Bellafaire/ESP32-Smart-Watch/Pictures and Videos/20191118_123628.jpg

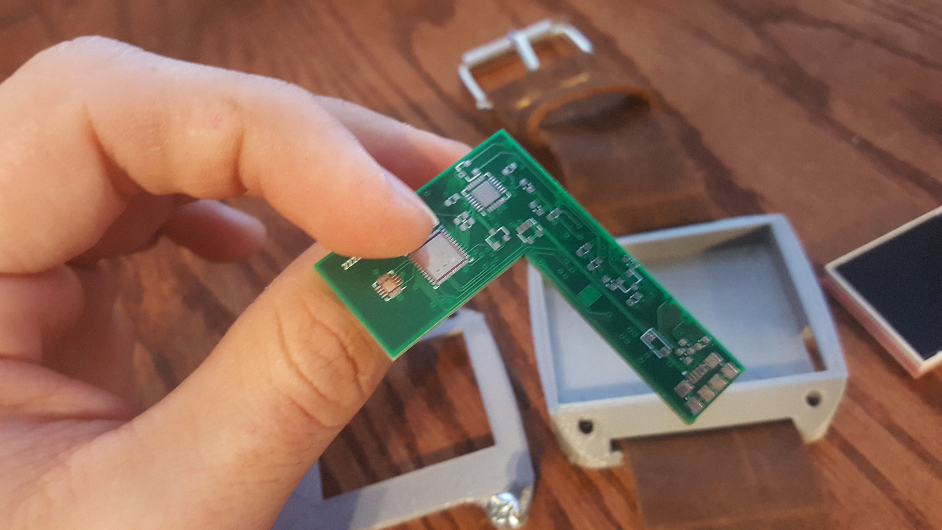
Pictures and Videos/20191118_123628.jpg
