Bellafaire/ESP32-Smart-Watch/Pictures and Videos/20191118_124004.jpg

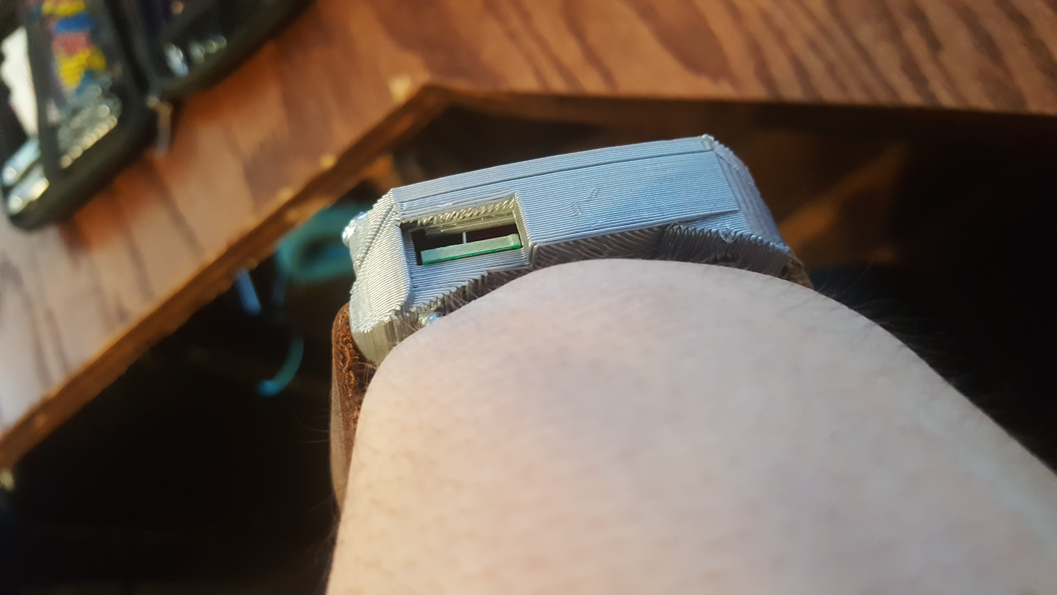
Pictures and Videos/20191118_124004.jpg
