Bellafaire/ESP32-Smart-Watch/Pictures and Videos/20200519_230237.jpg

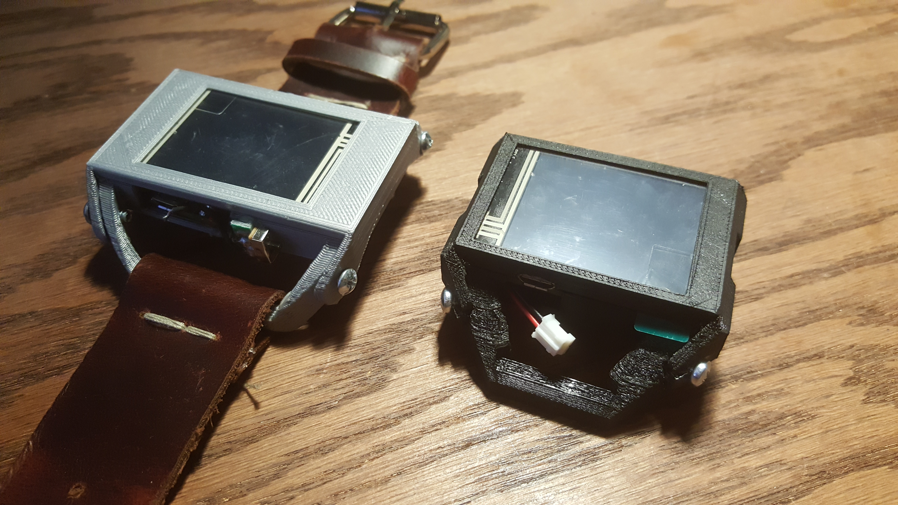
Pictures and Videos/20200519_230237.jpg
