Bellafaire/ESP32-Smart-Watch/Pictures and Videos/20200519_230911.jpg

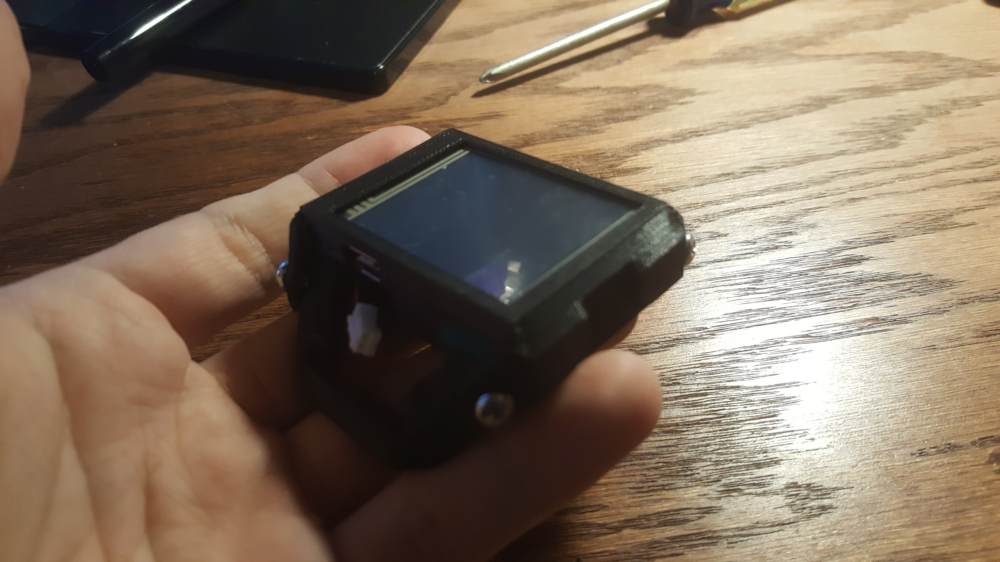
Pictures and Videos/20200519_230911.jpg
