Bellafaire/ESP32-Smart-Watch/Pictures and Videos/20200519_233520.jpg

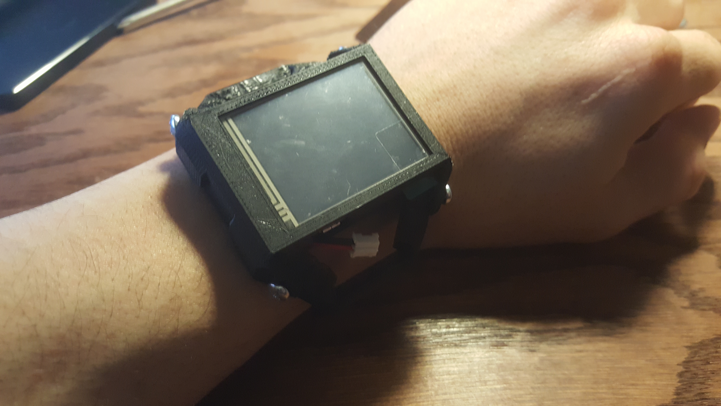
Pictures and Videos/20200519_233520.jpg
