Bellafaire/ESP32-Smart-Watch/Pictures and Videos/20200614_194343.jpg

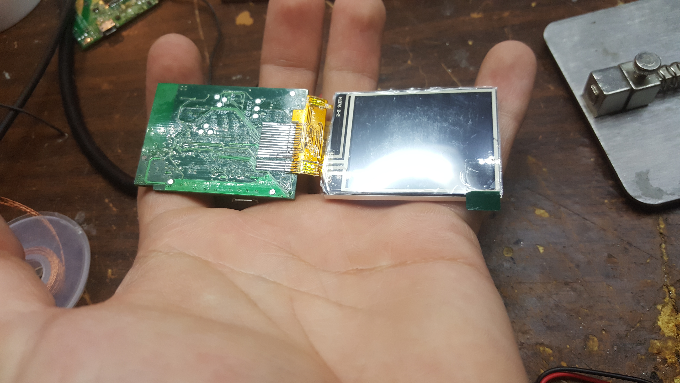
Pictures and Videos/20200614_194343.jpg
