Bellafaire/ESP32-Smart-Watch/Pictures and Videos/20200614_194347.jpg

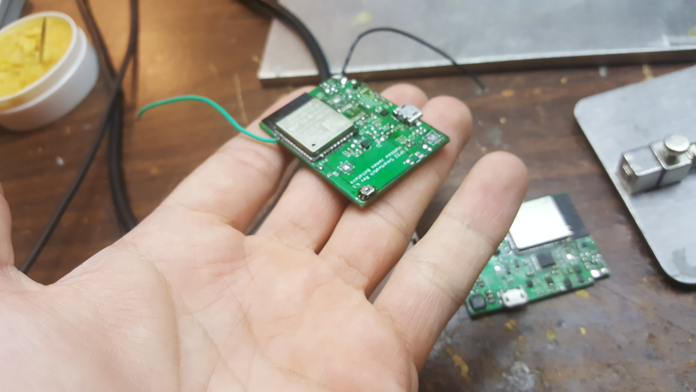
Pictures and Videos/20200614_194347.jpg
