Bellafaire/ESP32-Smart-Watch/Pictures and Videos/IMG_20200818_204534.jpg

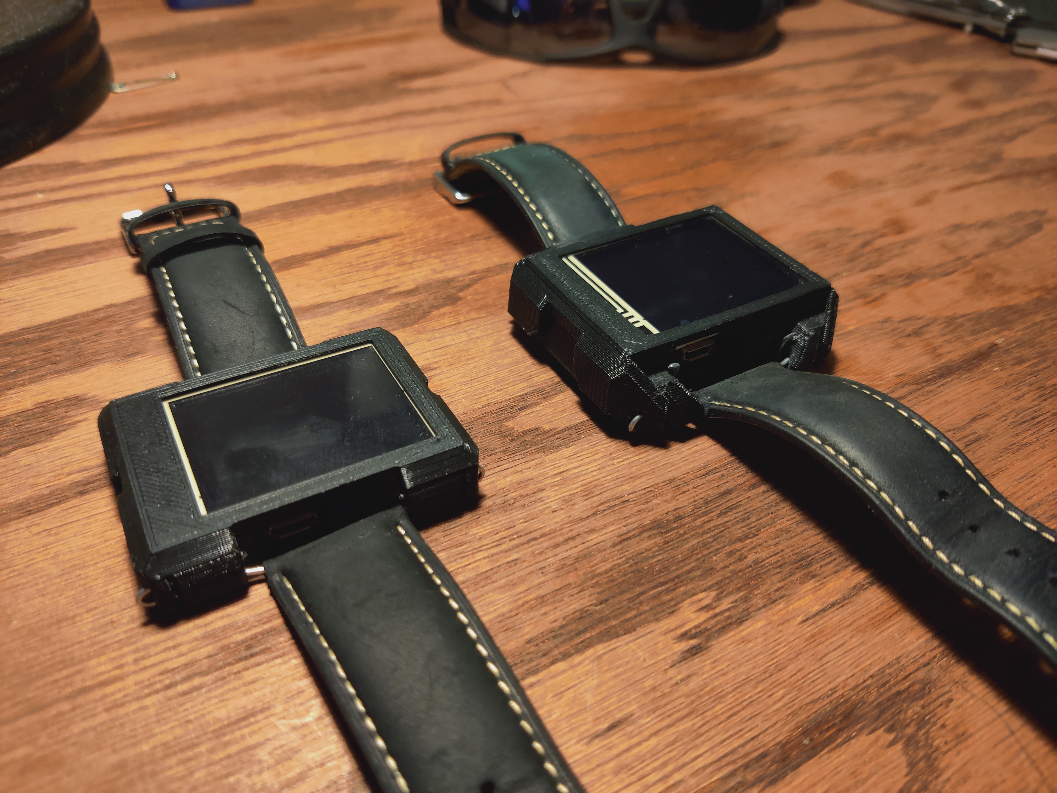
Pictures and Videos/IMG_20200818_204534.jpg
