Bellafaire/ESP32-Smart-Watch/Pictures and Videos/IMG_20200818_204633.jpg

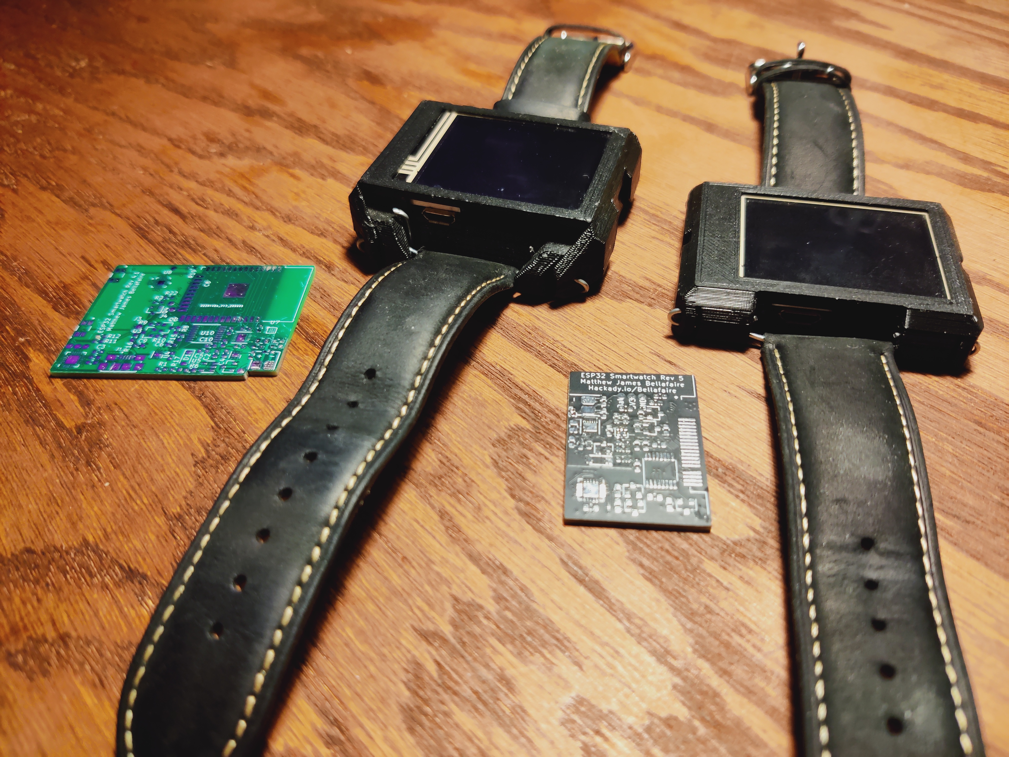
Pictures and Videos/IMG_20200818_204633.jpg
