Bellafaire/ESP32-Smart-Watch/Pictures and Videos/IMG_20200818_2127321.jpg

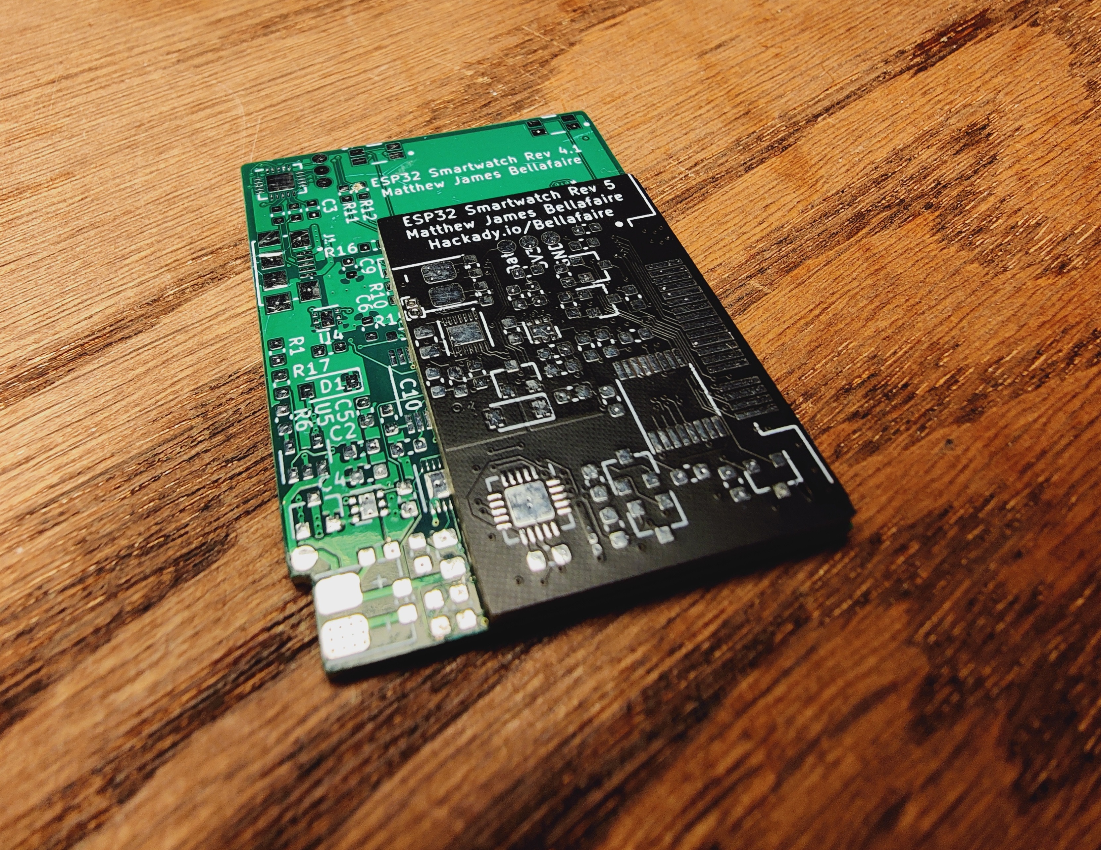
Pictures and Videos/IMG_20200818_2127321.jpg
