Bellafaire/ESP32-Smart-Watch/Pictures and Videos/Screenshot_1 (2).png

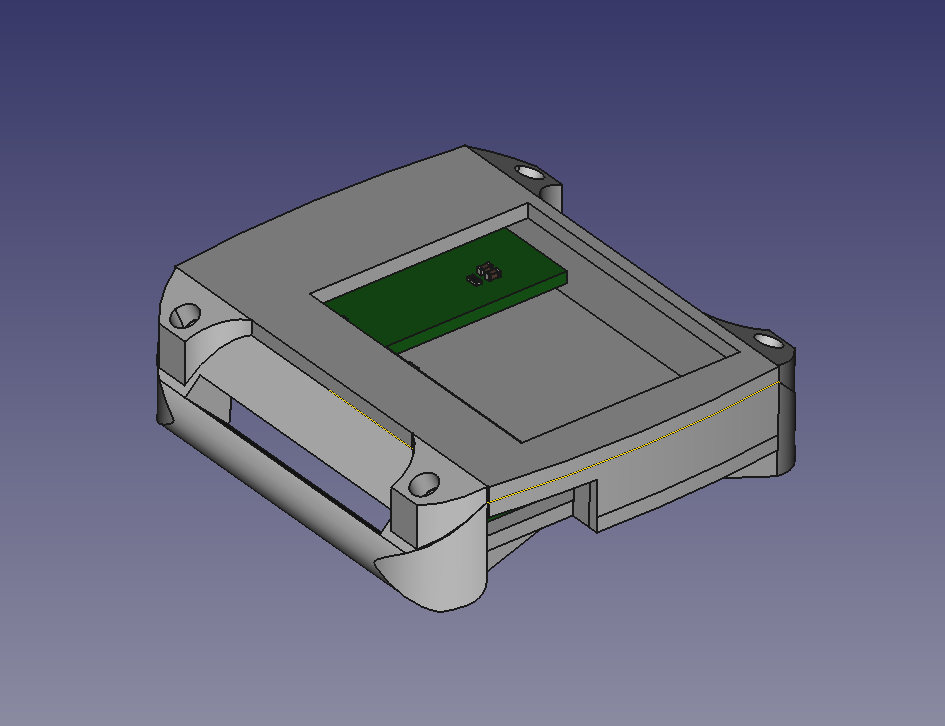
Pictures and Videos/Screenshot_1 (2).png
