Bellafaire/ESP32-Smart-Watch/Pictures and Videos/vlcsnap-2020-08-18-21h04m51s279.png

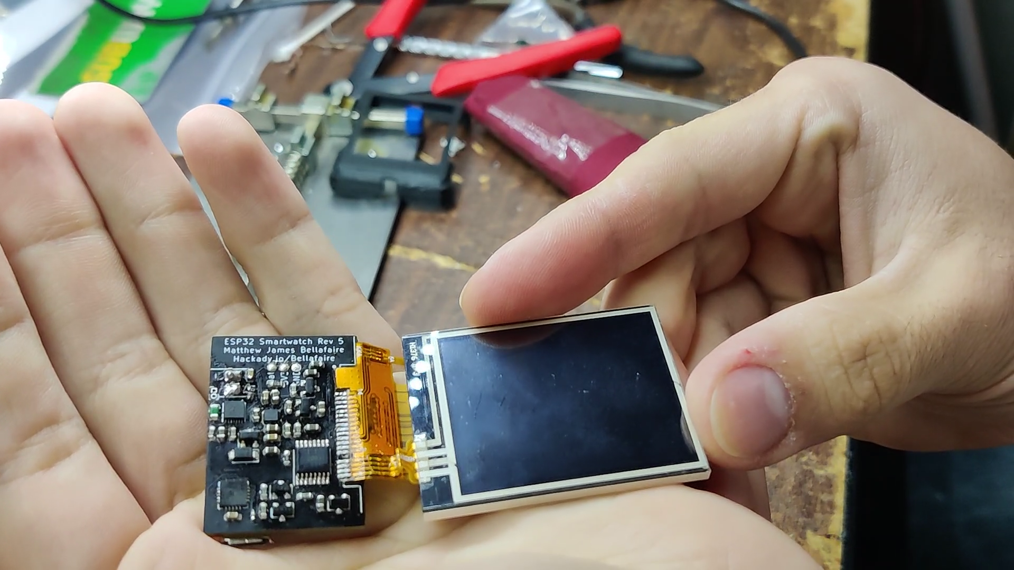
Pictures and Videos/vlcsnap-2020-08-18-21h04m51s279.png
