Bellafaire/ESP32-Smart-Watch/Smartwatch_Software_V3/Declarations.h

/*****************************************************************************
  The MIT License (MIT)
  Copyright (c) 2021 Matthew James Bellafaire
  Permission is hereby granted, free of charge, to any person obtaining a copy
  of this software and associated documentation files (the "Software"), to deal
  in the Software without restriction, including without limitation the rights
  to use, copy, modify, merge, publish, distribute, sublicense, and/or sell
  copies of the Software, and to permit persons to whom the Software is
  furnished to do so, subject to the following conditions:
  The above copyright notice and this permission notice shall be included in all
  copies or substantial portions of the Software.
  THE SOFTWARE IS PROVIDED "AS IS", WITHOUT WARRANTY OF ANY KIND, EXPRESS OR
  IMPLIED, INCLUDING BUT NOT LIMITED TO THE WARRANTIES OF MERCHANTABILITY,
  FITNESS FOR A PARTICULAR PURPOSE AND NONINFRINGEMENT. IN NO EVENT SHALL THE
  AUTHORS OR COPYRIGHT HOLDERS BE LIABLE FOR ANY CLAIM, DAMAGES OR OTHER
  LIABILITY, WHETHER IN AN ACTION OF CONTRACT, TORT OR OTHERWISE, ARISING FROM,
  OUT OF OR IN CONNECTION WITH THE SOFTWARE OR THE USE OR OTHER DEALINGS IN THE
  SOFTWARE.
******************************************************************************/

#ifndef DECLARATIONS
#define DECLARATIONS

#include <Adafruit_GFX.h>    // Core graphics library
#include <Adafruit_ST7735.h> // Hardware-specific library for ST7735
#include <Wire.h>
#include <EEPROM.h>
#include <soc/rtc.h>
#include <sys/time.h>
#include <driver/adc.h>
#include <math.h>

#include <BLEDevice.h>
#include <BLEUtils.h>
#include <BLEServer.h>
#include <BLE2902.h>
#include <esp_gatt_common_api.h>

// appicon depends
#include "base64.hpp"
#include "FS.h"
#include "SPIFFS.h"

/*******************************************************************
                              DEBUG
 *******************************************************************/
// prints debug information to the serial terminal when declared
#define DEBUG

#ifdef DEBUG
#define printDebug(a) Serial.println(a)
#endif
#ifndef DEBUG
#define printDebug(a)
#endif

/*******************************************************************
                            Signitures
 *******************************************************************/
// wakeup.ino
boolean wakeupCheck();

/*******************************************************************
                              Macros
 *******************************************************************/
#define RGB_TO_BGR565(r, g, b) ((((uint8_t)(b >> 3) & 0x001F) << 11) | (((uint8_t)(g >> 2) & 0x003F) << 5) | (((uint8_t)(r >> 3) & 0x001F)))

/********************************************************************
                        Notification Layout
 ********************************************************************/
#define NOTIFICATION_APP_NAME 0
#define NOTIFICATION_EXTRA_TEXT 1
#define NOTIFICATION_EXTRA_INFO 2
#define NOTIFICATION_EXTRA_SUB_TEXT 3
#define NOTIFICATION_EXTRA_TITLE 4
#define NOTIFICATION_DESCRIPTION 5

/********************************************************************
                            Calendar
 ********************************************************************/
#define CALENDAR_TITLE 0
#define CALENDAR_DESCRIPTION 1
#define CALENDAR_START_DATE 2
#define CALENDAR_START_TIME 3
#define CALENDAR_END_TIME 4
#define CALENDAR_EVENT_LOCATION 5

struct calendarEvent
{
  String title;
  String description;
  String date;
  int timeStart, timeEnd; // minutes of day
  String time;
  String location;
};

/*******************************************************************
                       Hardware Pin Declarations
 *******************************************************************/

// touch screen driver interrupt request
#define TOUCH_IRQ 4

// LCD pins
#define LCD_EN 13
#define LCD_CS 16
#define LCD_LED 14
#define LCD_SCK 18
#define LCD_DC 21 // LCD_A0
#define LCD_RST 22
#define LCD_MOSI 23

// power regulation/monitoring pins
//#define BAT_ALRT 34 //not used in v4.1
#define CHG_STAT 35
#define REG_PG 36
#define ACCEL_EN 34

// I2C Pins and Addresses
#define I2C_SCL 32
#define I2C_SDA 33
#define BAT_MONITOR_ADDR 0x36
#define TOUCH_ADDR 0x48

// Accelerometer connections (optional extra)
#define X_ACCEL 26
#define Y_ACCEL 27
#define Z_ACCEL 25

#define X_ACCEL_ADC_CH 9
#define Y_ACCEL_ADC_CH 7
#define Z_ACCEL_ADC_CH 8

/********************************************************************
                           LCD Objects
 ********************************************************************/
#define SCREEN_WIDTH 160
#define SCREEN_HEIGHT 128
Adafruit_ST7735 tft = Adafruit_ST7735(LCD_CS, LCD_DC, LCD_RST);
GFXcanvas16 *frameBuffer = new GFXcanvas16(SCREEN_WIDTH, SCREEN_HEIGHT);

#define CHARACTER_WIDTH 6
#define CHARACTER_HEIGHT 8

#define WINDOW_CHARACTER_WIDTH 6
#define WINDOW_CHARACTER_HEIGHT 8
#define WINDOW_FONT_SIZE 1

// great color picker here: https://www.wamingo.net/rgbbgr/
#define BACKGROUND_COLOR RGB_TO_BGR565(45, 9, 34)

#define TEXT_COLOR ST77XX_WHITE
#define INTERFACE_COLOR ST77XX_WHITE
#define GRAYED 0xBDF7
int ERROR_COLOR = ST77XX_BLUE;

#define LCD_BACKLIGHT_PWM_CHAN 0

/********************************************************************
                          SLEEP and Wake
 ********************************************************************/
// number of times per second the ESP32 will wake up to check the accelerometer
#define ACCELEROMETER_SLEEP_POLLING_PER_SECOND 4

#define ACCELEROMETER_STAY_AWAKE_THRESHOLD 2000

#define ACCELEROMETER_MAX_VALUE 4096
#define ACCELEROMETER_MIN_VALUE 0

// accelerometer value when the watch screen is perpendicular to the ground (screen facing away from body)
#define ACCEL_Y_DIP 2250
#define ACCEL_Z_DIP 1800

// accelerometer value when the watch is facing upwards, level with the ground
#define ACCEL_Y_VERT 1800
#define ACCEL_Z_VERT 2260

// threshold of the above values that will register a dip condition
// the threshold should be adjusted to suit the desired sensitivity, there's not really a method to it just try out some values.
#define DIP_THRESHOLD 0.05
#define DIP_THRESHOLD_VALUE (ACCELEROMETER_MAX_VALUE - ACCELEROMETER_MIN_VALUE) * DIP_THRESHOLD

// macros, for the wakeup function, just to compress the if statements so they're a bit easier to read.
// true if screen is pointed up
#define isUp(y, z) (ACCEL_Y_VERT < y + DIP_THRESHOLD_VALUE && ACCEL_Y_VERT > y - DIP_THRESHOLD_VALUE && ACCEL_Z_VERT < z + DIP_THRESHOLD_VALUE && ACCEL_Z_VERT > z - DIP_THRESHOLD_VALUE)
// true if screen is pointed away from user and perpendicular to the ground
#define isDown(y, z) (ACCEL_Y_DIP < y + DIP_THRESHOLD_VALUE && ACCEL_Y_DIP > y - DIP_THRESHOLD_VALUE && ACCEL_Z_DIP < z + DIP_THRESHOLD_VALUE && ACCEL_Z_DIP > z - DIP_THRESHOLD_VALUE)

#define TAP_WAKE_TIME 3000

#define TIMER_SLEEP_TIME 1000000ULL / ACCELEROMETER_SLEEP_POLLING_PER_SECOND

/********************************************************************
                          Globals
 ********************************************************************/
String notificationData = "";
String currentSong = "Reading From Phone...";
unsigned long lastSongUpdate = 0;

/********************************************************************
                            TOUCH
 ********************************************************************/
RTC_DATA_ATTR boolean CLEAR_TOUCH_CALIBRATION = false;

#define TOTAL_CALIBRATION_POINTS 4

// define location of calibration points.
const int CALIBRATION_POINTS_X[TOTAL_CALIBRATION_POINTS] = {
    SCREEN_WIDTH / 4,
    3 * SCREEN_WIDTH / 4,
    SCREEN_WIDTH / 4,
    3 * SCREEN_WIDTH / 4};

const int CALIBRATION_POINTS_Y[TOTAL_CALIBRATION_POINTS] = {
    SCREEN_HEIGHT / 4,
    SCREEN_HEIGHT / 4,
    3 * SCREEN_HEIGHT / 4,
    3 * SCREEN_HEIGHT / 4};

// defines whether or not touch handling will occur in as a result of the touch handling ISR or
// happen in the main thread.
//  #define USE_TOUCH_HANDLING_TASK

struct point
{
  int x = -1;
  int y = -1;
};

volatile unsigned long lastTouchTime = 0;

TaskHandle_t xTouch = NULL;

/********************************************************************
                  Battery Monitor Configuration
         These declarations are specific to the revision
         5 of the smartwatch design, if the battery size
         were increased or the sense resistor value was
         changed these values would need to be adjusted
 ********************************************************************/
//#define designcap 1200 //600mAh (0.5mAh resolution / 600mAh) (for 10m sense resistor)
#define designcap 480 // 240mAh (240mAh /0.5mAh resolution ) (for 10m sense resistor)
#define ichgterm 20
#define vempty 0x9650
#define modelcfg 0x8400

/********************************************************************
                            timeKeeping
 ********************************************************************/
RTC_DATA_ATTR struct tm *timeinfo;

/********************************************************************
                            DataSeperators
 ********************************************************************/
#define FIELD_SEPARATOR ';'
#define FIELD_SEPARATOR_STRING ";"

#define optionDivider '`' // change this to anything you don't think will be used
#define SELECTION_WINDOW_BUTTON_WIDTH 20

/********************************************************************
                           EEPROM SETTINGS
 ********************************************************************/
#define EEPROM_SIZE 512

// EEPROM Data locations and information
// eeprom allocations for data placement and their corrosponding string for display.
#define DAYLIGHT_SAVINGS 1
#define WAKEUP_TYPE DAYLIGHT_SAVINGS + 1
#define SCREEN_BRIGHTNESS WAKEUP_TYPE + 1

// touch calibration
#define CALIBRATION_X1 SCREEN_BRIGHTNESS + 1
#define CALIBRATION_X2 CALIBRATION_X1 + 2
#define CALIBRATION_X3 CALIBRATION_X2 + 2
#define CALIBRATION_X4 CALIBRATION_X3 + 2

#define CALIBRATION_Y1 CALIBRATION_X4 + 2
#define CALIBRATION_Y2 CALIBRATION_Y1 + 2
#define CALIBRATION_Y3 CALIBRATION_Y2 + 2
#define CALIBRATION_Y4 CALIBRATION_Y3 + 2

// variables that are pulled from the eeprom on wakeup
byte SETTING_DAYLIGHT_SAVINGS = 0;
byte SETTING_WAKEUP_TYPE = 0;
byte SETTING_SCREEN_BRIGHTNESS = 0;
uint16_t calibrationX[4];
uint16_t calibrationY[4];

// wakeup type defines
#define WAKEUP_TOUCH_ONLY 0
#define WAKEUP_ACCELEROMETER 1
#define WAKEUP_ACCELEROMTER_DISPLAY_TIME 2

/********************************************************************
                              BLE
 ********************************************************************/
// variables and defines used by BLEServer.ino
static String currentDataField;
static boolean blockingCommandInProgress = false;
static String *bleReturnString;
#define SERVICE_UUID "5ac9bc5e-f8ba-48d4-8908-98b80b566e49"
#define COMMAND_UUID "bcca872f-1a3e-4491-b8ec-bfc93c5dd91a"
BLECharacteristic *commandCharacteristic;
BLEService *pService;
BLEServer *pServer;
TaskHandle_t xBLE = NULL;

// indicates connection state to the android device
static boolean connected = false;

// indiciates whether or not a operation is currently in progress
static boolean operationInProgress = false;

// function signitures
// String sendBLE(String command);
boolean sendBLE(String command, String *returnString, boolean blocking);
void addData(String data); // adds data to a current string, used within BLEServer.ino
void initBLE();            // initializes the BLE connection by starting advertising.

/********************************************************************
                        Drawable manager
 ********************************************************************/

// maximum number of drawables allowed (this number determines the number of pointers, so it can be large)
#define MAX_DRAWABLES 128

// swipe
#define SWIPE_RIGHT 1
#define SWIPE_UP 0
#define SWIPE_LEFT 3
#define SWIPE_DOWN 2

// threshold of movement required for a swipe to be detected.
#define SWIPE_DISTANCE_THRESHOLD 60

/*Icons for buttons and other visual elements */
//"play.bmp" width=16 height=16
const uint16_t PLAY_MEDIA_ICON_16X16[] PROGMEM = {0x0000, 0x0000, 0x0000, 0x0000, 0x0000, 0x0000, 0x0000, 0x0000, 0x0000, 0x0000, 0x0000, 0x0000, 0x0000, 0x0000, 0x0000, 0x0000,
                                                  0x0000, 0x0000, 0x0000, 0x0000, 0xFFFF, 0xFFFF, 0x0000, 0x0000, 0x0000, 0x0000, 0x0000, 0x0000, 0x0000, 0x0000, 0x0000, 0x0000,
                                                  0x0000, 0x0000, 0x0000, 0x0000, 0xFFFF, 0xFFFF, 0xFFFF, 0x0000, 0x0000, 0x0000, 0x0000, 0x0000, 0x0000, 0x0000, 0x0000, 0x0000,
                                                  0x0000, 0x0000, 0x0000, 0x0000, 0xFFFF, 0xFFFF, 0xFFFF, 0xFFFF, 0x0000, 0x0000, 0x0000, 0x0000, 0x0000, 0x0000, 0x0000, 0x0000,
                                                  0x0000, 0x0000, 0x0000, 0x0000, 0xFFFF, 0xFFFF, 0xFFFF, 0xFFFF, 0xFFFF, 0x0000, 0x0000, 0x0000, 0x0000, 0x0000, 0x0000, 0x0000,
                                                  0x0000, 0x0000, 0x0000, 0x0000, 0xFFFF, 0xFFFF, 0xFFFF, 0xFFFF, 0xFFFF, 0xFFFF, 0x0000, 0x0000, 0x0000, 0x0000, 0x0000, 0x0000,
                                                  0x0000, 0x0000, 0x0000, 0x0000, 0xFFFF, 0xFFFF, 0xFFFF, 0xFFFF, 0xFFFF, 0xFFFF, 0xFFFF, 0x0000, 0x0000, 0x0000, 0x0000, 0x0000,
                                                  0x0000, 0x0000, 0x0000, 0x0000, 0xFFFF, 0xFFFF, 0xFFFF, 0xFFFF, 0xFFFF, 0xFFFF, 0xFFFF, 0xFFFF, 0x0000, 0x0000, 0x0000, 0x0000,
                                                  0x0000, 0x0000, 0x0000, 0x0000, 0xFFFF, 0xFFFF, 0xFFFF, 0xFFFF, 0xFFFF, 0xFFFF, 0xFFFF, 0xFFFF, 0x0000, 0x0000, 0x0000, 0x0000,
                                                  0x0000, 0x0000, 0x0000, 0x0000, 0xFFFF, 0xFFFF, 0xFFFF, 0xFFFF, 0xFFFF, 0xFFFF, 0xFFFF, 0x3068, 0x0000, 0x0000, 0x0000, 0x0000,
                                                  0x0000, 0x0000, 0x0000, 0x0000, 0xFFFF, 0xFFFF, 0xFFFF, 0xFFFF, 0xFFFF, 0xFFFF, 0x3068, 0x0000, 0x0000, 0x0000, 0x0000, 0x0000,
                                                  0x0000, 0x0000, 0x0000, 0x0000, 0xFFFF, 0xFFFF, 0xFFFF, 0xFFFF, 0xFFFF, 0x3068, 0x0000, 0x0000, 0x0000, 0x0000, 0x0000, 0x0000,
                                                  0x0000, 0x0000, 0x0000, 0x0000, 0xFFFF, 0xFFFF, 0xFFFF, 0xFFFF, 0x3068, 0x0000, 0x0000, 0x0000, 0x0000, 0x0000, 0x0000, 0x0000,
                                                  0x0000, 0x0000, 0x0000, 0x0000, 0xFFFF, 0xFFFF, 0xFFFF, 0x3068, 0x0000, 0x0000, 0x0000, 0x0000, 0x0000, 0x0000, 0x0000, 0x0000,
                                                  0x0000, 0x0000, 0x0000, 0x0000, 0xFFFF, 0xFFFF, 0x3068, 0x0000, 0x0000, 0x0000, 0x0000, 0x0000, 0x0000, 0x0000, 0x0000, 0x0000,
                                                  0x0000, 0x0000, 0x0000, 0x0000, 0x0000, 0x3068, 0x0000, 0x0000, 0x0000, 0x0000, 0x0000, 0x0000, 0x0000, 0x0000, 0x0000, 0x0000};
//"pause.bmp" width=16 height=16
const uint16_t PAUSE_MEDIA_ICON_16X16[] PROGMEM = {0x0000, 0x0000, 0x0000, 0x0000, 0x0000, 0x0000, 0x0000, 0x0000, 0x0000, 0x0000, 0x0000, 0x0000, 0x0000, 0x0000, 0x0000, 0x0000,
                                                   0x0000, 0xFFFF, 0xFFFF, 0xFFFF, 0xFFFF, 0xFFFF, 0xFFFF, 0x0000, 0x0000, 0xFFFF, 0xFFFF, 0xFFFF, 0xFFFF, 0xFFFF, 0xFFFF, 0x0000,
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
*/
#endif
