Bellafaire/ESP32-Smart-Watch/SmartWatch_Software/IconButtons.h

/*****************************************************************************
The MIT License (MIT)

Copyright (c) 2020 Matthew James Bellafaire

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
THE SOFTWARE IS PROVIDED "AS IS", WITHOUT WARRANTY OF ANY KIND, EXPRESS OR
IMPLIED, INCLUDING BUT NOT LIMITED TO THE WARRANTIES OF MERCHANTABILITY,
FITNESS FOR A PARTICULAR PURPOSE AND NONINFRINGEMENT. IN NO EVENT SHALL THE
AUTHORS OR COPYRIGHT HOLDERS BE LIABLE FOR ANY CLAIM, DAMAGES OR OTHER
LIABILITY, WHETHER IN AN ACTION OF CONTRACT, TORT OR OTHERWISE, ARISING FROM,
OUT OF OR IN CONNECTION WITH THE SOFTWARE OR THE USE OR OTHER DEALINGS IN THE
SOFTWARE.
******************************************************************************/
PROGMEM iconButton homeButton = {128, 96, 32, 32, INTERFACE_COLOR, BACKGROUND_COLOR, {(0b00000000 << 8) | 0b00000000, (0b00000000 << 8) | 0b00000000, (0b00000001 << 8) | 0b10000000, (0b00000011 << 8) | 0b11000000, (0b00000111 << 8) | 0b11100000, (0b00001111 << 8) | 0b11110000, (0b00111111 << 8) | 0b11111100, (0b01111111 << 8) | 0b11111110, (0b11111111 << 8) | 0b11111111, (0b00111111 << 8) | 0b11111100, (0b00111110 << 8) | 0b00111100, (0b00111110 << 8) | 0b00111100, (0b00111110 << 8) | 0b00111100, (0b00111110 << 8) | 0b00111100, (0b00111110 << 8) | 0b00111100, (0b00000000 << 8) | 0b00000000}};
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
    (0b11111110 << 8) | 0b11111110,
    (0b01111110 << 8) | 0b01111110,
    (0b00111110 << 8) | 0b00111110,
    (0b00011110 << 8) | 0b00011110,
    (0b00001110 << 8) | 0b00001110,
    (0b00000110 << 8) | 0b00000110,
    (0b00000010 << 8) | 0b00000010,
    (0b00000000 << 8) | 0b00000000
  }
};
