Bellafaire/ESP32-Smart-Watch/SmartWatch_Software/MainLoop.h

/*  everything that happens in the normal operation of the smartwatch happens here. this is kind of the user-interface part of the code.  
 */
void MainLoop()
{
  testScreen();
}

void testScreen()
{
  tft.setTextColor(TEXT_COLOR);
  tft.setCursor(0, 0);
  tft.println("ESP32 Smartwatch");

  tft.print("Battery Percentage: ");
  tft.print(getBatteryPercentage());
  tft.println("%");

  tft.print("Battery Voltage: ");
  tft.print(getBatteryVoltage());
  tft.println("V");

  pinMode(CHG_STAT, INPUT);
  tft.print("Charging Status: ");
  tft.println(digitalRead(CHG_STAT));

  for (int a = 0; a < 5000; a++)
  {
    readTouch();
    delay(1);
  }
}
