Bellafaire/ESP32-Smart-Watch/Smartwatch_Software_V3/drawable.h

#include <Adafruit_GFX.h>
#ifndef DRAWABLE
#define DRAWABLE

class Drawable
{
public:
    Drawable(int x, int y, int width, int height, GFXcanvas16 *buffer_ptr);
    Drawable(int x, int y, int width, int height, GFXcanvas16 *buffer_ptr, String type);
    virtual void draw();
    int getx();
    int gety();
    int getWidth();
    int getHeight();
    int setDims(int x, int y, int width, int height); 
    virtual boolean isTouched(int x, int y);
    void setTouchable(boolean val);
    void registerCallback(void (*cb)());
    virtual void onTouch(int x, int y);
    String toString(); 

protected:
    String _type = "Drawable";
    int _x;
    int _y;
    int _width;
    int _height;
    int _ptouchx, _ptouchy;
    void (*_callback)() = nullptr;
    boolean _touchable = false;
    boolean _touched = false; //holds the value resulting from the last isTouched() call. 
    GFXcanvas16 *_buffer_ptr;
};
#endif
