Bellafaire/ESP32-Smart-Watch/Pictures and Videos/20191109_104612.jpg

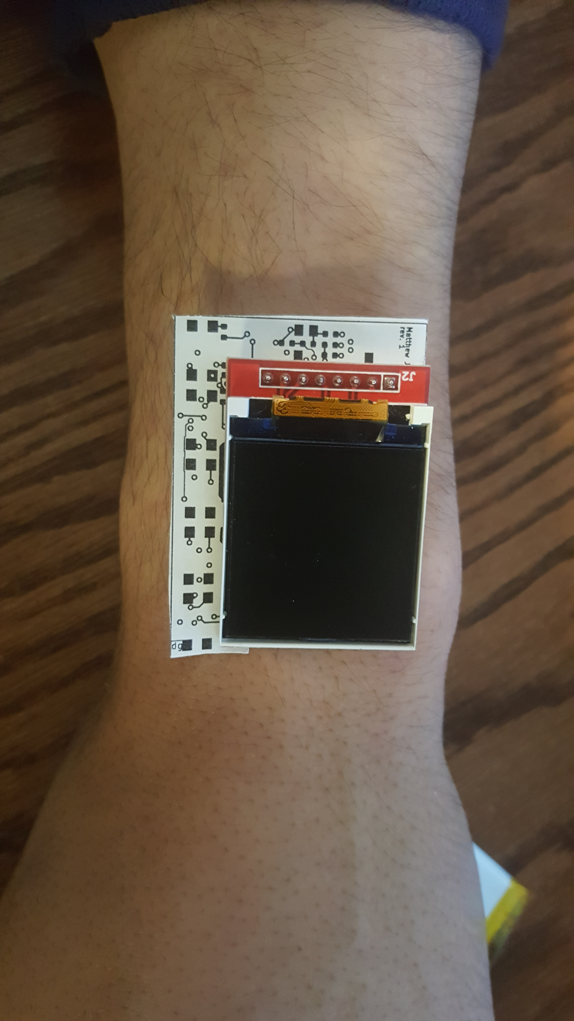
Pictures and Videos/20191109_104612.jpg
