Bellafaire/ESP32-Smart-Watch/Pictures and Videos/20200614_194340.jpg

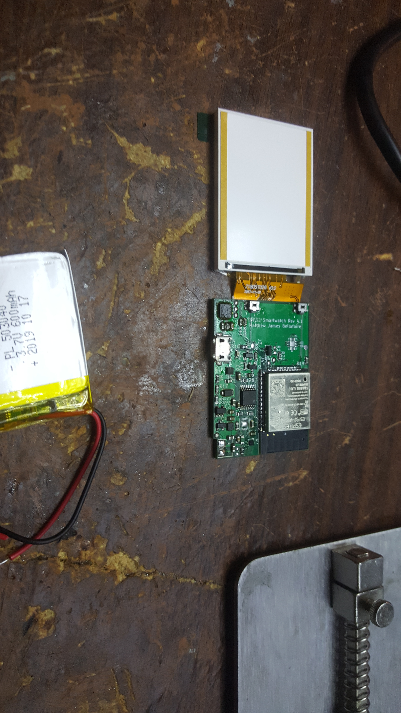
Pictures and Videos/20200614_194340.jpg
