Bellafaire/ESP32-Smart-Watch/Pictures and Videos/20200614_220425.jpg

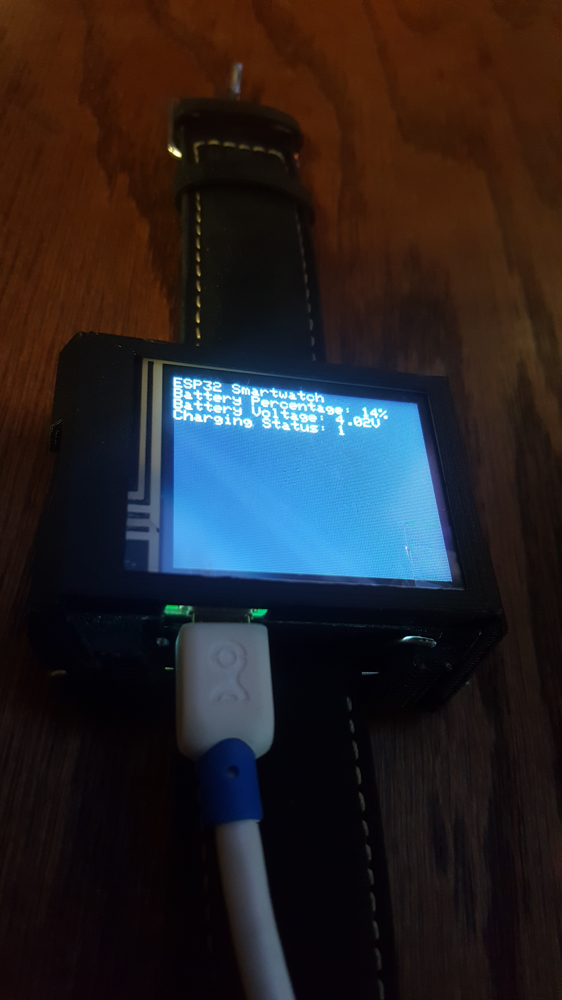
Pictures and Videos/20200614_220425.jpg
